theheliumlabs/solox5-revenge/raw/20240716_181724.jpg

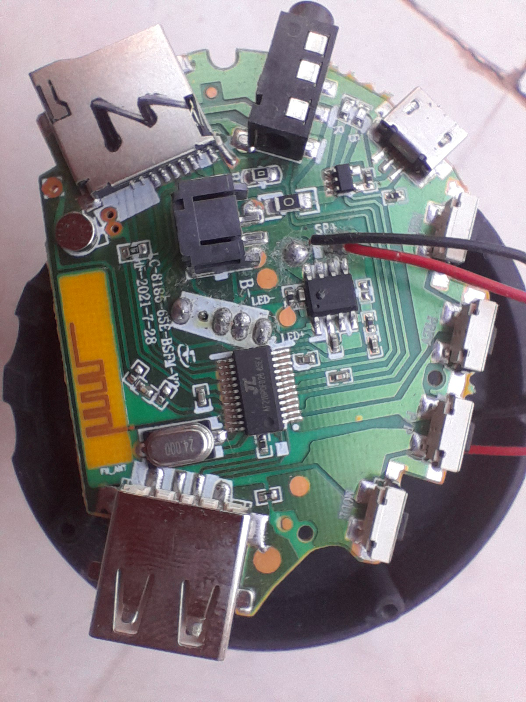
raw/20240716_181724.jpg
