theheliumlabs/solox5-revenge/raw/20240716_181734.jpg

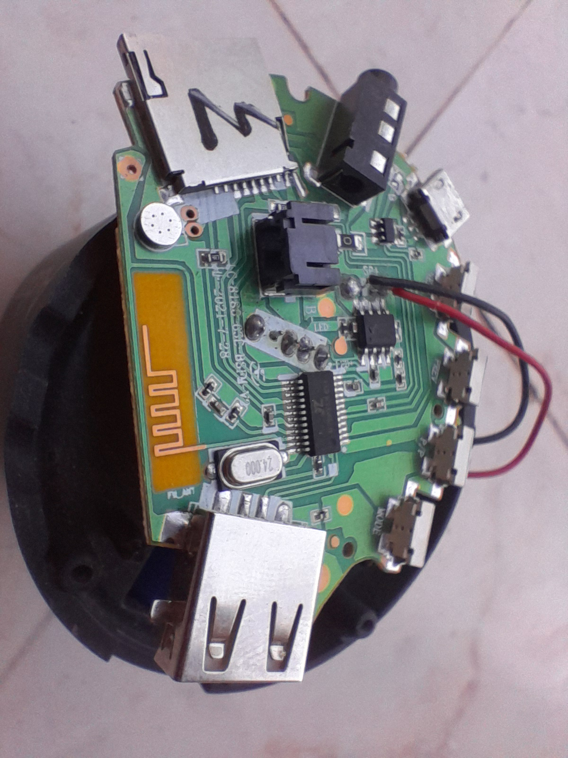
raw/20240716_181734.jpg
