theheliumlabs/solox5-revenge/raw/20240716_181743.jpg

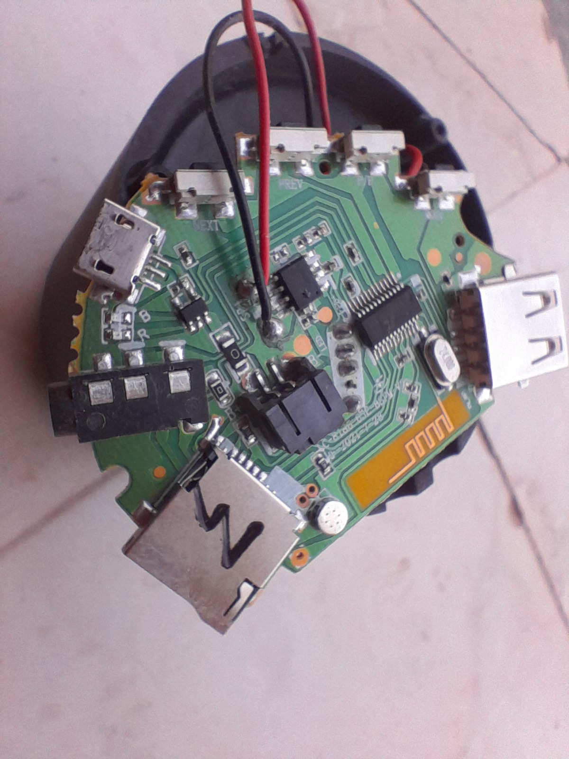
raw/20240716_181743.jpg
